Synthetic-Automated-Systems/open_micro_pump/pump1_1/parts_files/STL/6 peristaltic pump stator.stl

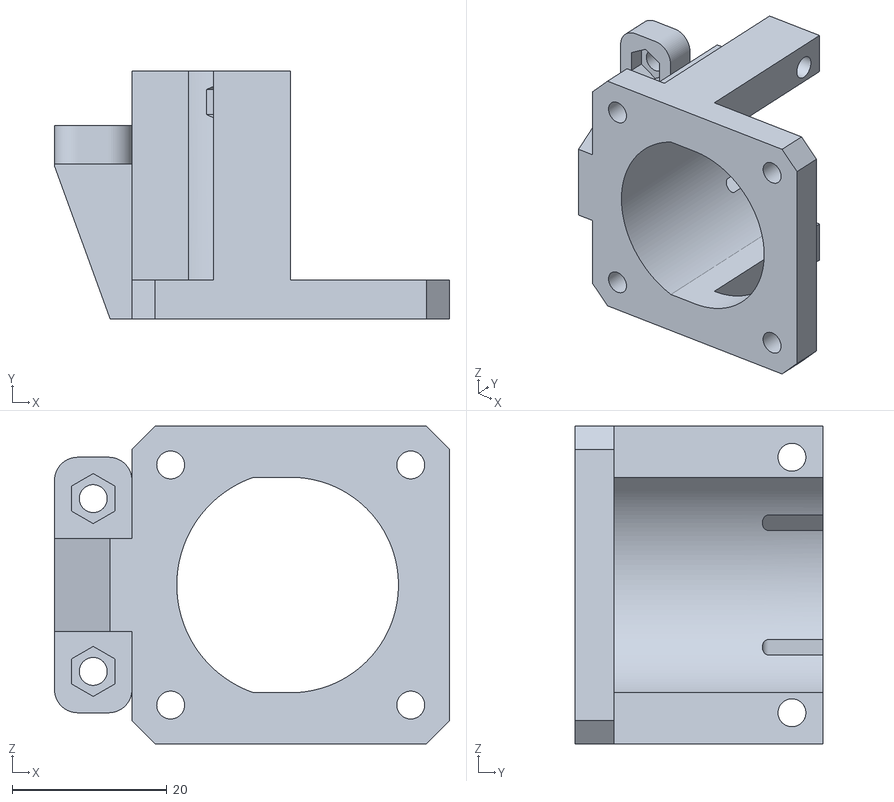
[picture p17: CAD file, 2022-01-19]
pump1_1/parts_files/STL/6 peristaltic pump stator.stl
51.0 x 32.0 x 41.0
