Synthetic-Automated-Systems/open_micro_pump/pump1_1/parts_files/STL/8 peristaltic pump clamp 0.3mm.stl

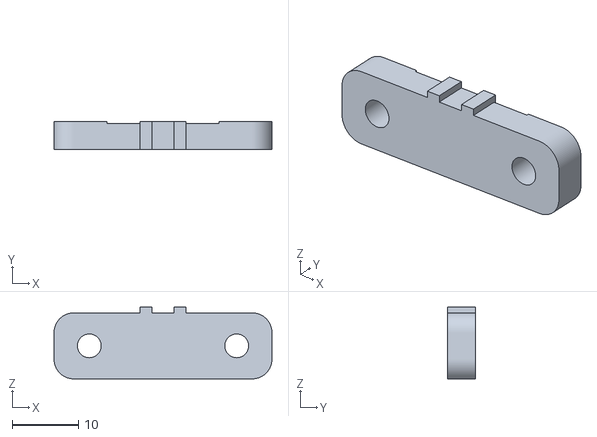
[picture p18: CAD file, 2022-01-19]
pump1_1/parts_files/STL/8 peristaltic pump clamp 0.3mm.stl
33.0 x 4.30 x 10.9
