Synthetic-Automated-Systems/open_micro_pump/pump1_1/parts_files/STL/shaft pusher top.stl

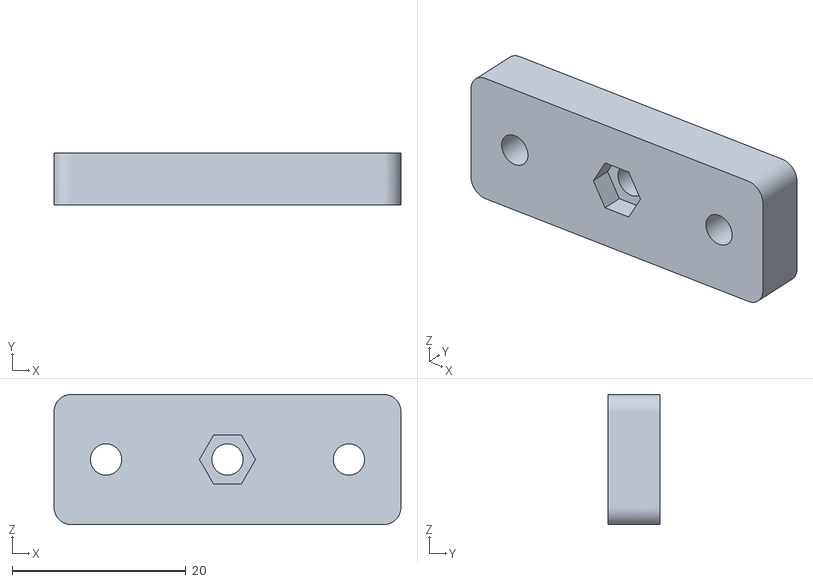
[picture p19: CAD file, 2022-01-19]
pump1_1/parts_files/STL/shaft pusher top.stl
40.0 x 6.00 x 15.0
