Synthetic-Automated-Systems/open_micro_pump/pump1_1/parts_files/STL/10 electronics lid.stl

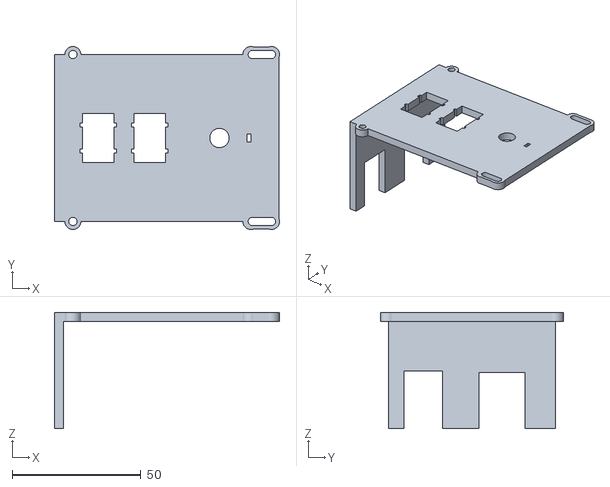
[picture p20: CAD file, 2022-01-19]
pump1_1/parts_files/STL/10 electronics lid.stl
87.3 x 71.0 x 45.1
